64860/IOT-THING/Images/back.jpg

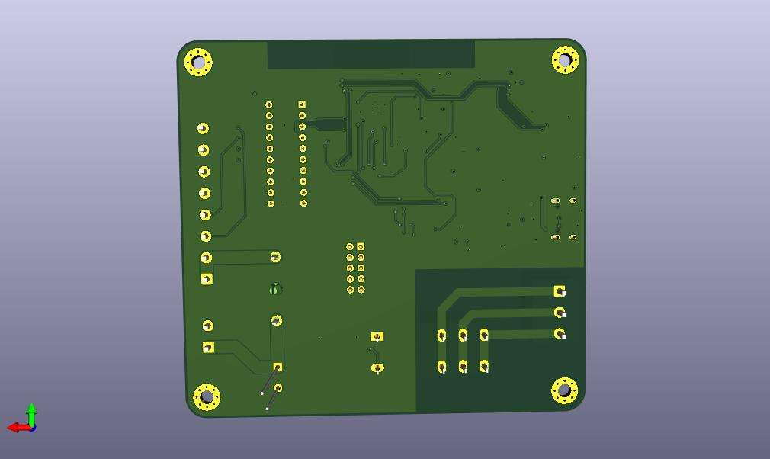
Images/back.jpg
