64860/IOT-THING/Images/pcbnew1.jpg

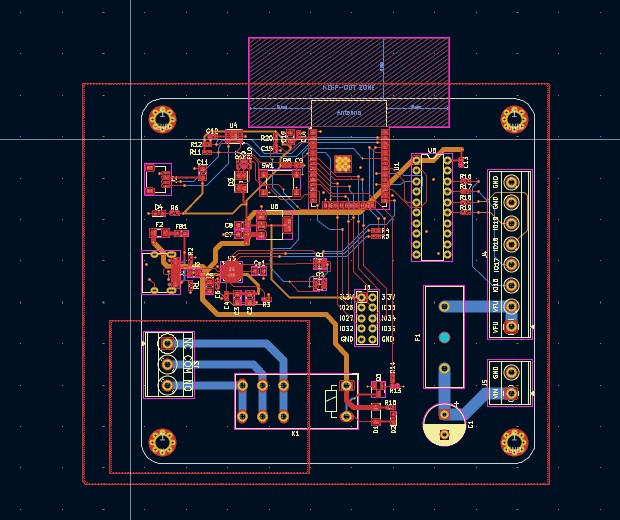
Images/pcbnew1.jpg
